Apollo917/3d-desk-shelf/_materials/covers/model-1-1.jpeg

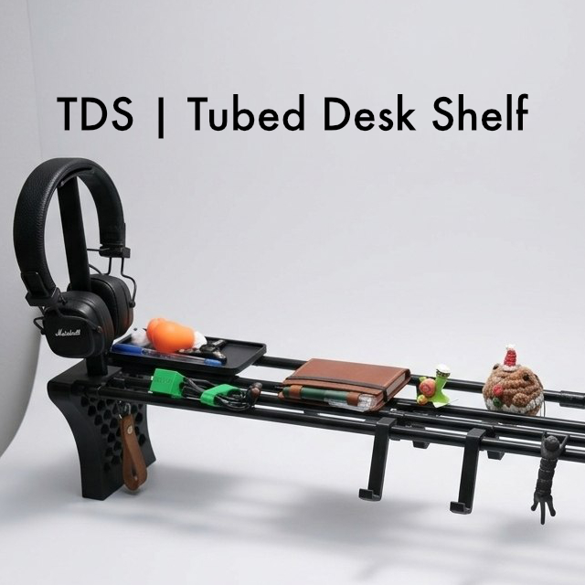
_materials/covers/model-1-1.jpeg
