Apollo917/3d-desk-shelf/_materials/covers/model-3-4.jpeg

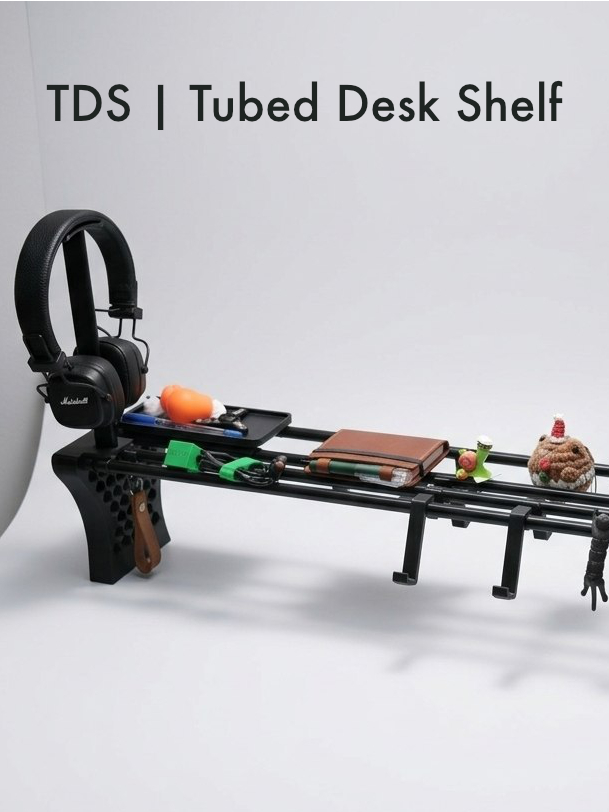
_materials/covers/model-3-4.jpeg
